Laasax/programme-spirob/Ressources/Electronique/Image1.png

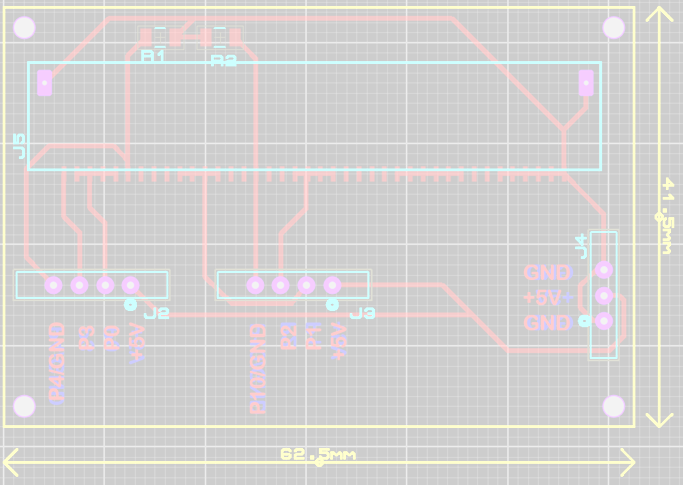
Ressources/Electronique/Image1.png
