Laasax/programme-spirob/Ressources/Fichiers 3D/poulie/20250404_160940.jpg

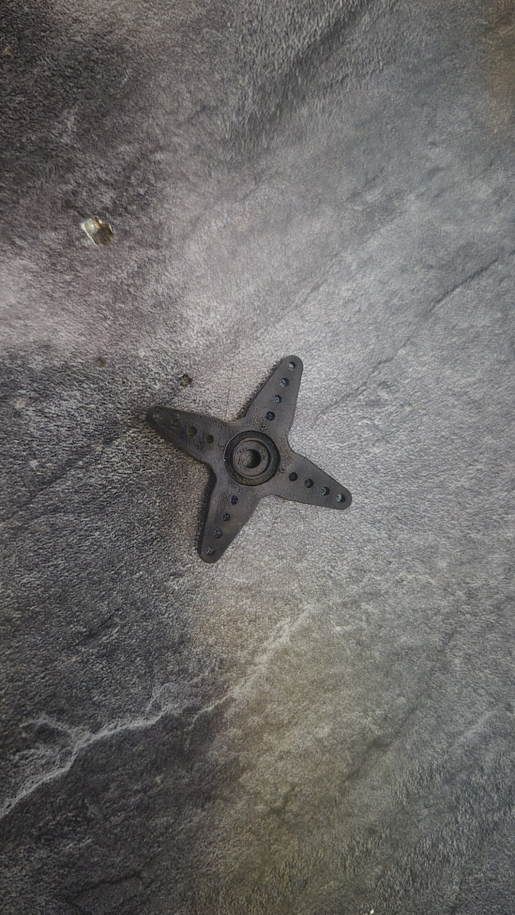
Ressources/Fichiers 3D/poulie/20250404_160940.jpg
