Laasax/programme-spirob/Ressources/Fichiers 3D/poulie/20250404_194326.jpg

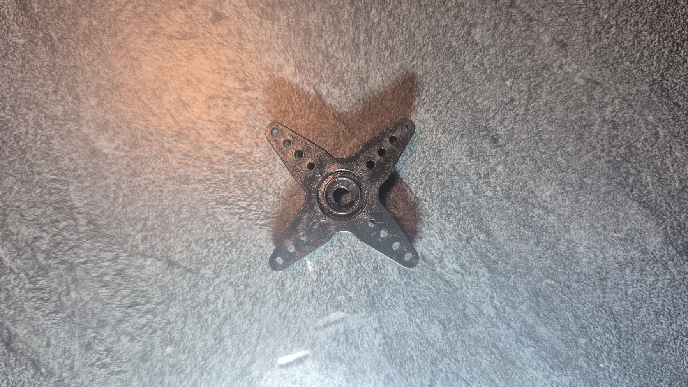
Ressources/Fichiers 3D/poulie/20250404_194326.jpg
