Laasax/programme-spirob/Ressources/Fichiers 3D/micro bit/assemblage carte micro bit et carte moteur.SLDASM

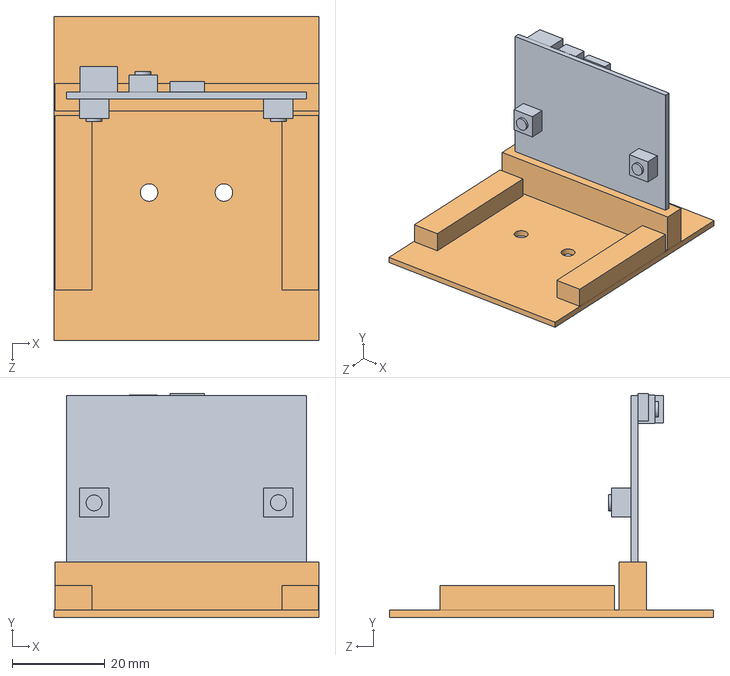
[picture p21: CAD file, 2025-06-08]
Ressources/Fichiers 3D/micro bit/assemblage carte micro bit et carte moteur.SLDASM
57.1 x 48.4 x 69.9 mm
carte moteur micro bit
carte microbit
