Laasax/programme-spirob/Ressources/Fichiers 3D/servomoteur/SolidWorks 2014/FS5109M_Ensemble arbre.SLDASM

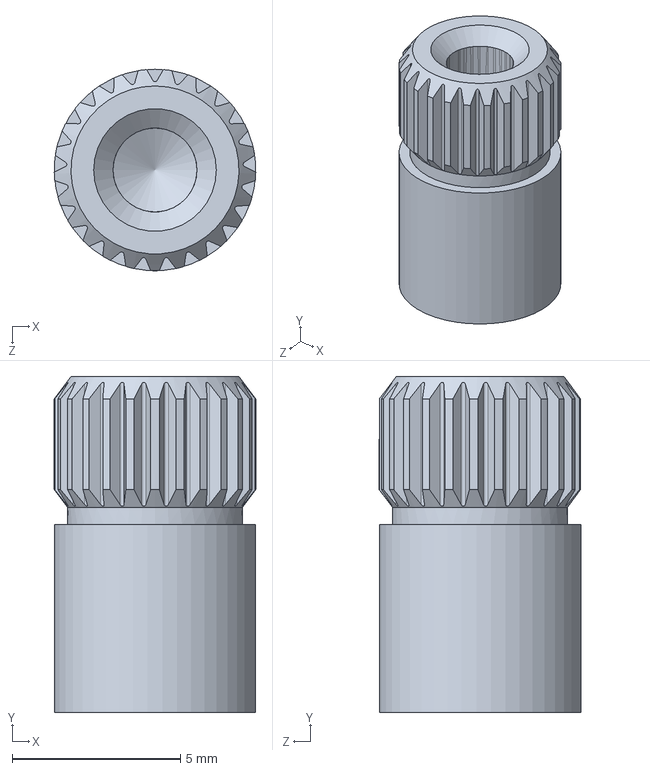
[picture p22: CAD file, 2025-06-08]
Ressources/Fichiers 3D/servomoteur/SolidWorks 2014/FS5109M_Ensemble arbre.SLDASM
6.00 x 10.00 x 6.00 mm
