Laasax/programme-spirob/Ressources/Fichiers 3D/micro bit/carte microbit.SLDPRT

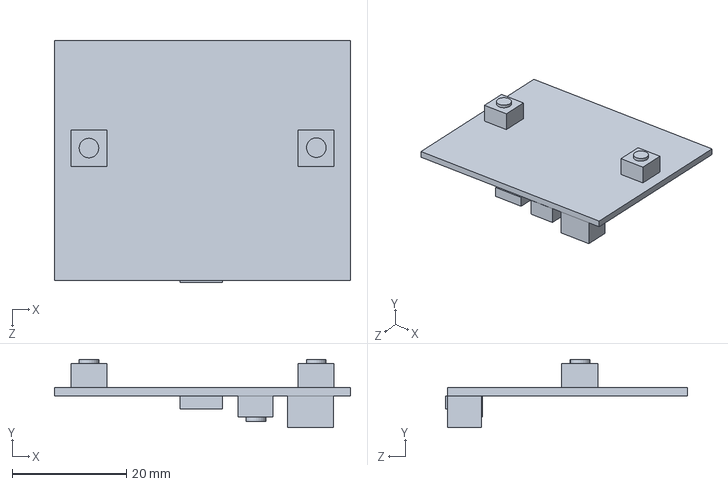
[picture p31: CAD file, 2025-06-08]
Ressources/Fichiers 3D/micro bit/carte microbit.SLDPRT
51.8 x 11.9 x 42.4 mm
