Laasax/programme-spirob/Ressources/Fichiers 3D/poulie/poulie servo.SLDPRT

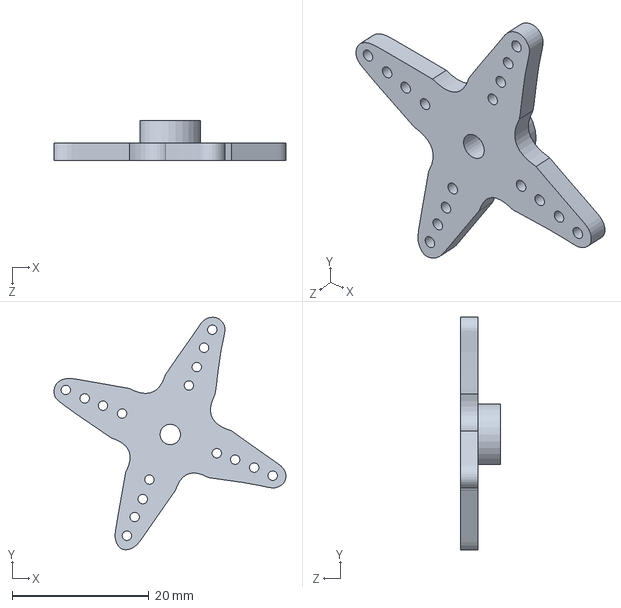
[picture p32: CAD file, 2025-06-08]
Ressources/Fichiers 3D/poulie/poulie servo.SLDPRT
34.0 x 34.1 x 5.82 mm
