Laasax/programme-spirob/Ressources/Fichiers 3D/servomoteur/SolidWorks 2014/FS5109M_palo 2S.SLDPRT

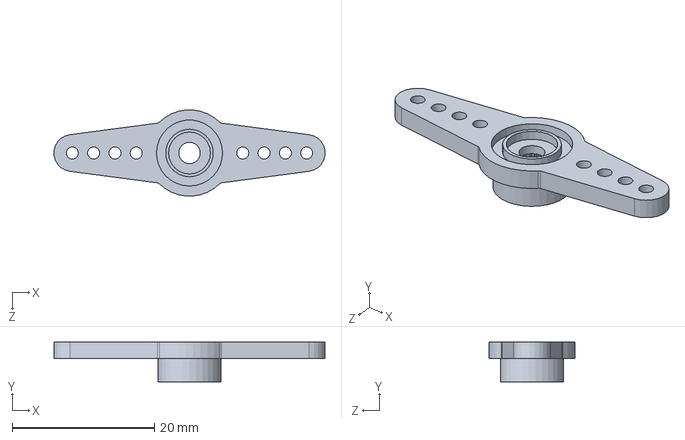
[picture p33: CAD file, 2025-06-08]
Ressources/Fichiers 3D/servomoteur/SolidWorks 2014/FS5109M_palo 2S.SLDPRT
38.2 x 5.60 x 12.1 mm
