Laasax/programme-spirob/Ressources/Fichiers 3D/STL/coque.STL

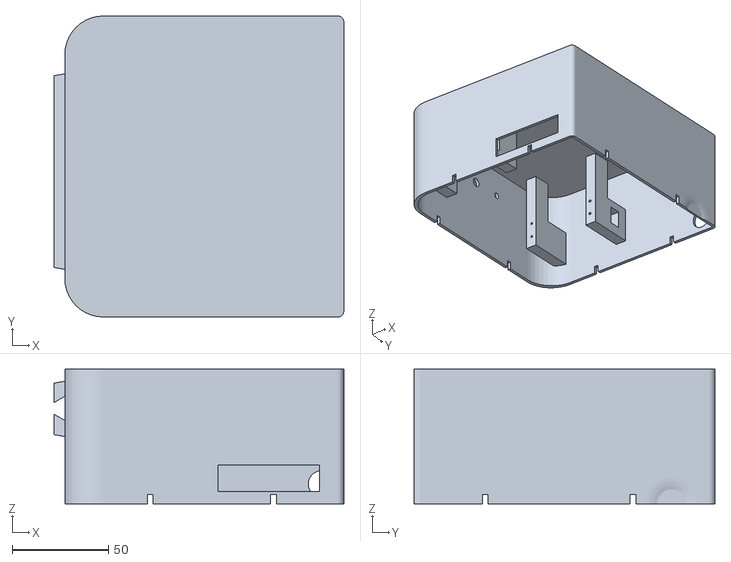
[picture p34: CAD file, 2025-06-08]
Ressources/Fichiers 3D/STL/coque.STL
150.4 x 156.3 x 70.0
