Laasax/programme-spirob/Ressources/Fichiers 3D/STL/2-cable SpiRob.STL

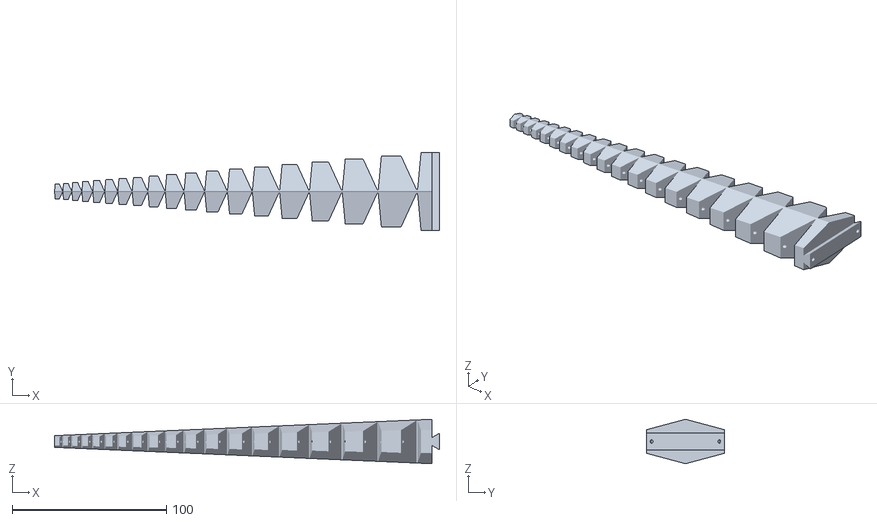
[picture p35: CAD file, 2025-06-08]
Ressources/Fichiers 3D/STL/2-cable SpiRob.STL
249.7 x 50.6 x 28.8
