Laasax/programme-spirob/Ressources/Fichiers 3D/micro bit/carte moteur micro bit.SLDPRT

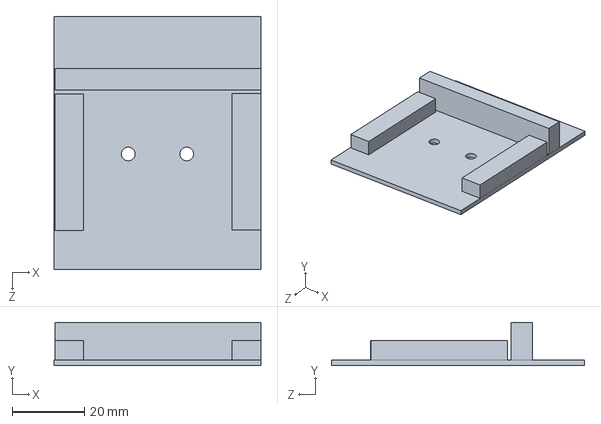
[picture p36: CAD file, 2025-06-08]
Ressources/Fichiers 3D/micro bit/carte moteur micro bit.SLDPRT
57.1 x 12.0 x 69.9 mm
