Laasax/programme-spirob/Ressources/Fichiers 3D/servomoteur/SolidWorks 2014/FS5109M_corps.SLDPRT

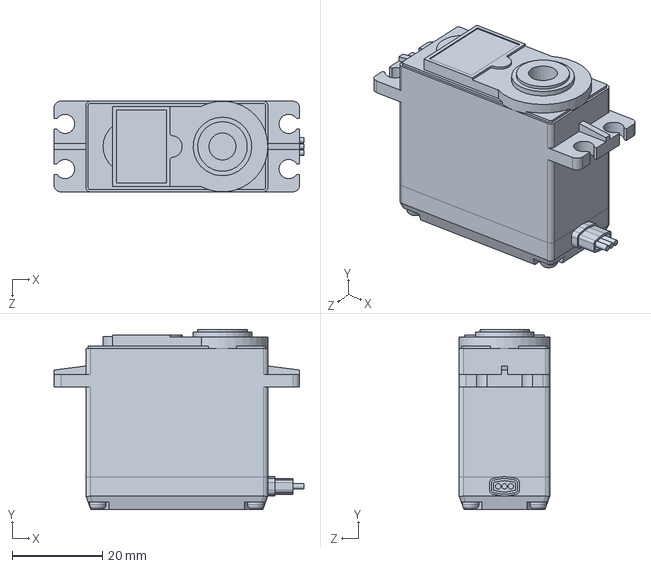
[picture p37: CAD file, 2025-06-08]
Ressources/Fichiers 3D/servomoteur/SolidWorks 2014/FS5109M_corps.SLDPRT
55.3 x 39.9 x 20.1 mm
