Laasax/programme-spirob/Ressources/Fichiers 3D/servomoteur/SolidWorks 2014/FS5109M_palo C.SLDPRT

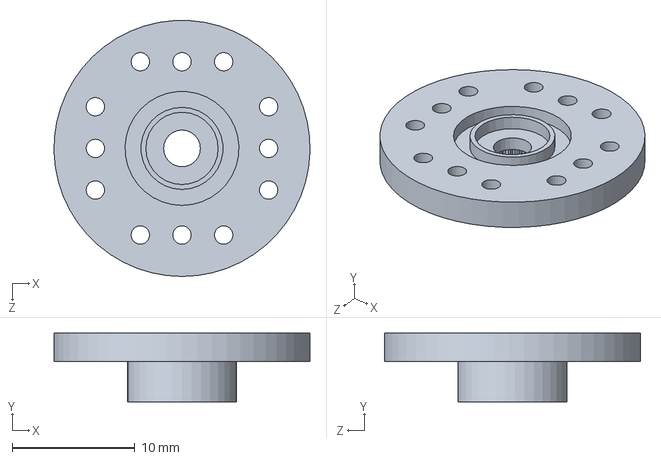
[picture p38: CAD file, 2025-06-08]
Ressources/Fichiers 3D/servomoteur/SolidWorks 2014/FS5109M_palo C.SLDPRT
20.9 x 5.60 x 20.9 mm
