Laasax/programme-spirob/Ressources/Fichiers 3D/servomoteur/SolidWorks 2014/FS5109M_palo 6.SLDPRT

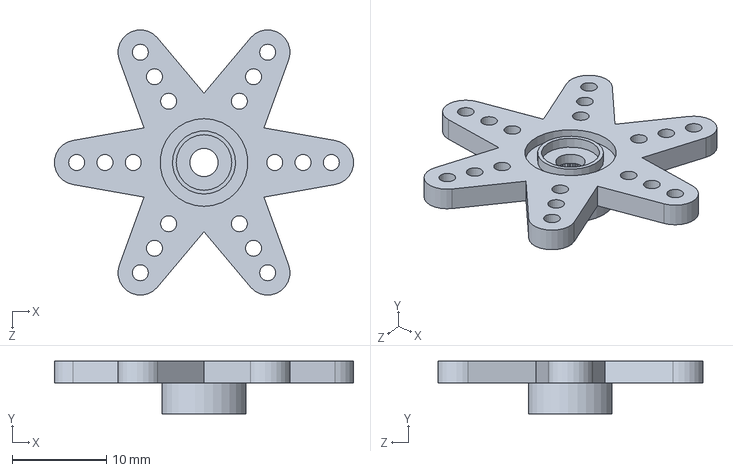
[picture p39: CAD file, 2025-06-08]
Ressources/Fichiers 3D/servomoteur/SolidWorks 2014/FS5109M_palo 6.SLDPRT
31.7 x 5.60 x 28.1 mm
