Laasax/programme-spirob/Ressources/Fichiers 3D/servomoteur/SolidWorks 2014/FS5109M_palo 4.SLDPRT

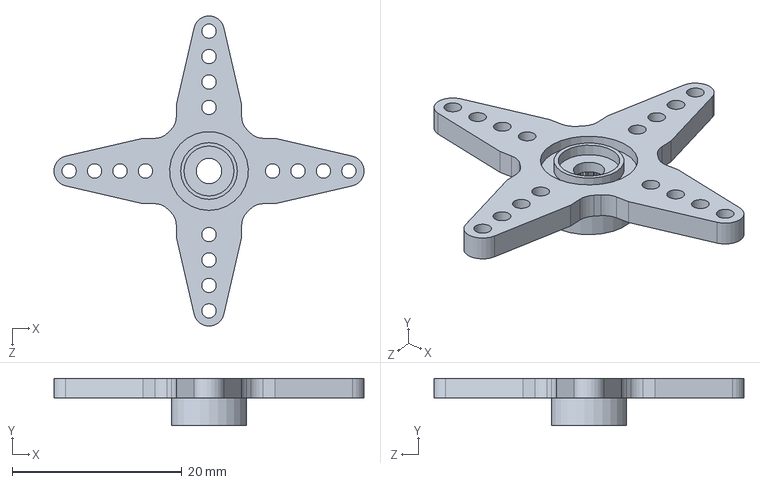
[picture p40: CAD file, 2025-06-08]
Ressources/Fichiers 3D/servomoteur/SolidWorks 2014/FS5109M_palo 4.SLDPRT
36.6 x 5.60 x 36.6 mm
