Laasax/programme-spirob/Ressources/Fichiers 3D/servomoteur/SolidWorks 2014/FS5109M_vis arbre M3 x 6.SLDPRT

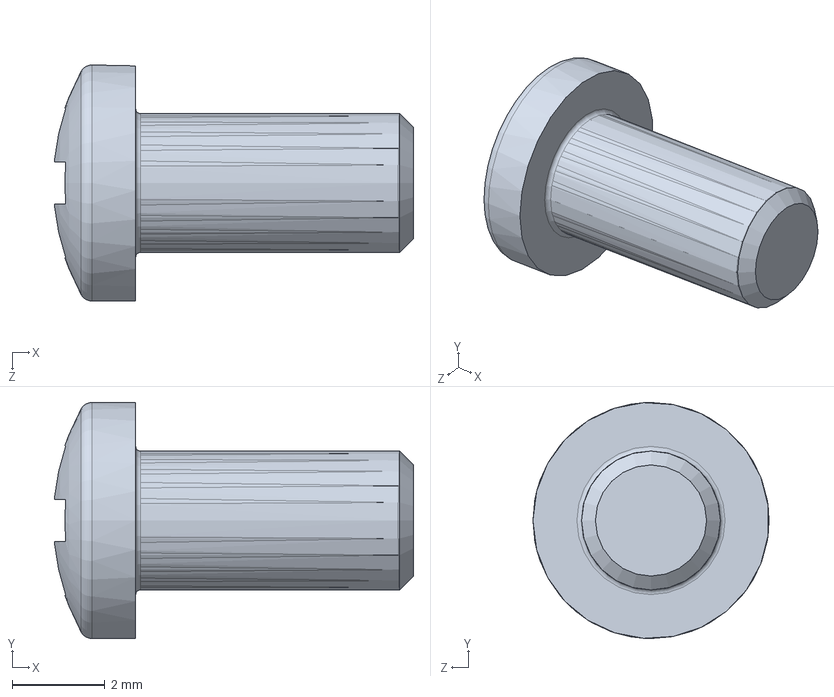
[picture p41: CAD file, 2025-06-08]
Ressources/Fichiers 3D/servomoteur/SolidWorks 2014/FS5109M_vis arbre M3 x 6.SLDPRT
7.75 x 5.10 x 5.10 mm
