Laasax/programme-spirob/Ressources/Fichiers 3D/servomoteur/SolidWorks 2014/FS5109M_silent-bloc_douille.SLDPRT

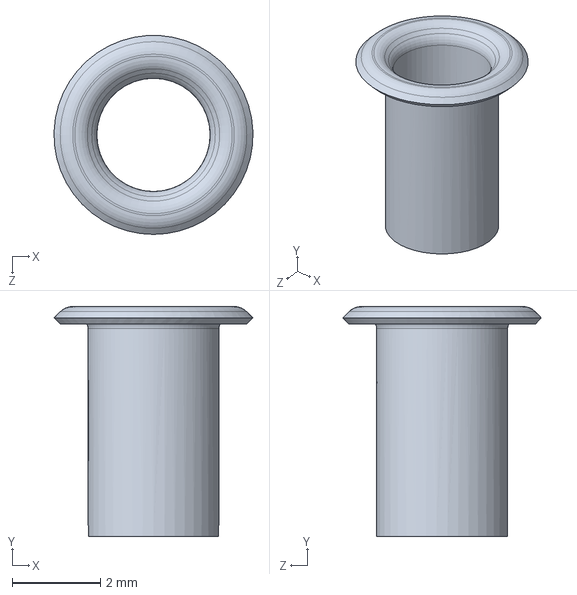
[picture p42: CAD file, 2025-06-08]
Ressources/Fichiers 3D/servomoteur/SolidWorks 2014/FS5109M_silent-bloc_douille.SLDPRT
4.50 x 5.20 x 4.49 mm
