Laasax/programme-spirob/Ressources/Fichiers 3D/servomoteur/SolidWorks 2014/FS5109M_vis servo 2 x 10.SLDPRT

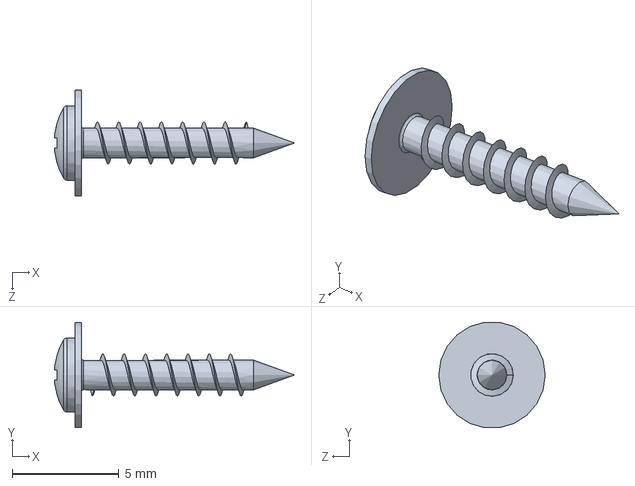
[picture p43: CAD file, 2025-06-08]
Ressources/Fichiers 3D/servomoteur/SolidWorks 2014/FS5109M_vis servo 2 x 10.SLDPRT
11.3 x 4.95 x 5.00 mm
