Laasax/programme-spirob/Ressources/Fichiers 3D/servomoteur/SolidWorks 2014/FS5109M_palo 2B.SLDPRT

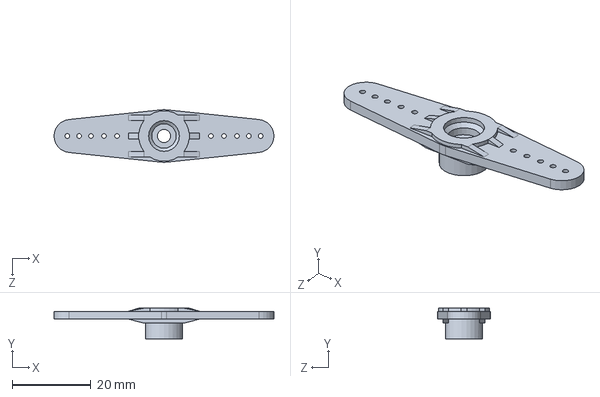
[picture p44: CAD file, 2025-06-08]
Ressources/Fichiers 3D/servomoteur/SolidWorks 2014/FS5109M_palo 2B.SLDPRT
55.7 x 7.80 x 13.3 mm
