Laasax/programme-spirob/Ressources/Fichiers 3D/servomoteur/SolidWorks 2014/FS5109M_silent-bloc.SLDPRT

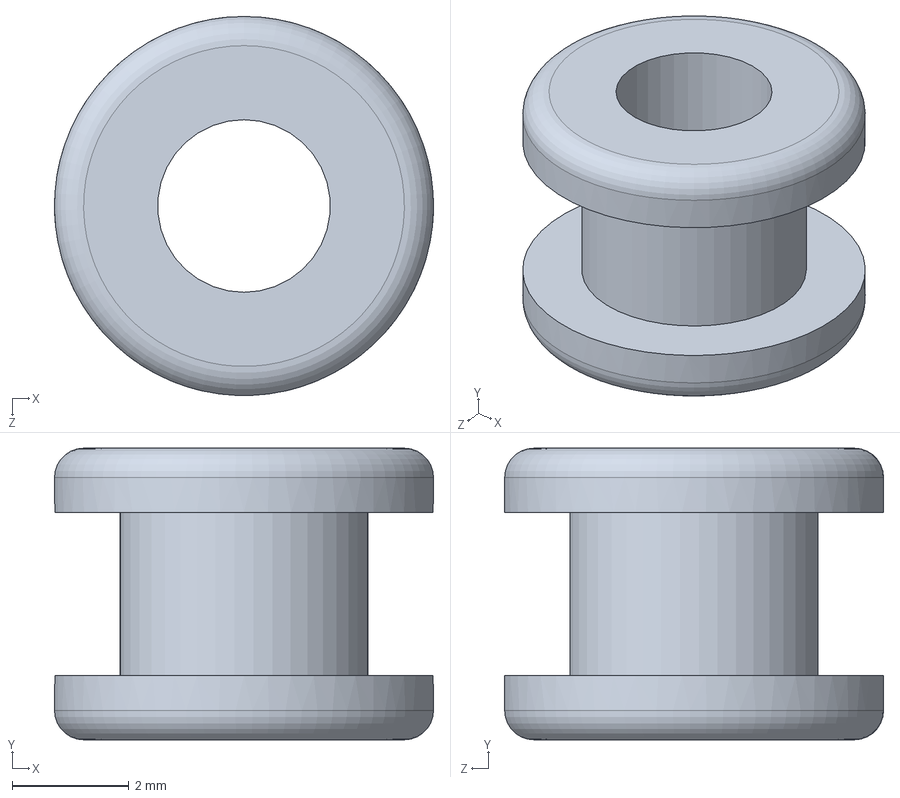
[picture p45: CAD file, 2025-06-08]
Ressources/Fichiers 3D/servomoteur/SolidWorks 2014/FS5109M_silent-bloc.SLDPRT
6.50 x 5.00 x 6.50 mm
